DoctorBeryl/Braillescan-Mesh-Translator/braille-scan-1785328133079/img-1785328105541.jpg

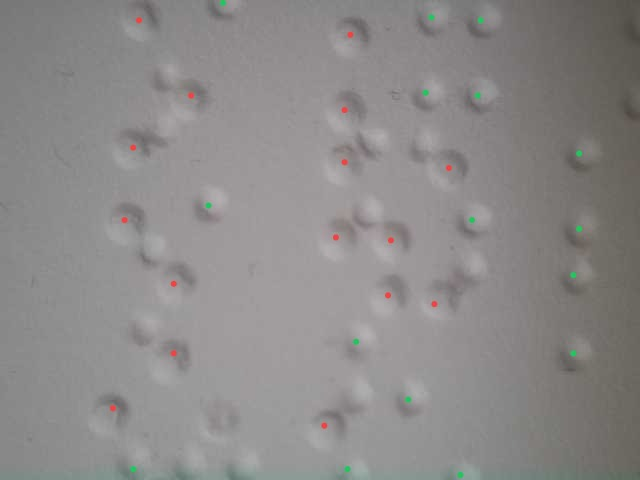
braille-scan-1785328133079/img-1785328105541.jpg
