DoctorBeryl/Braillescan-Mesh-Translator/braille-stitched-fixed/piece_0007.jpg

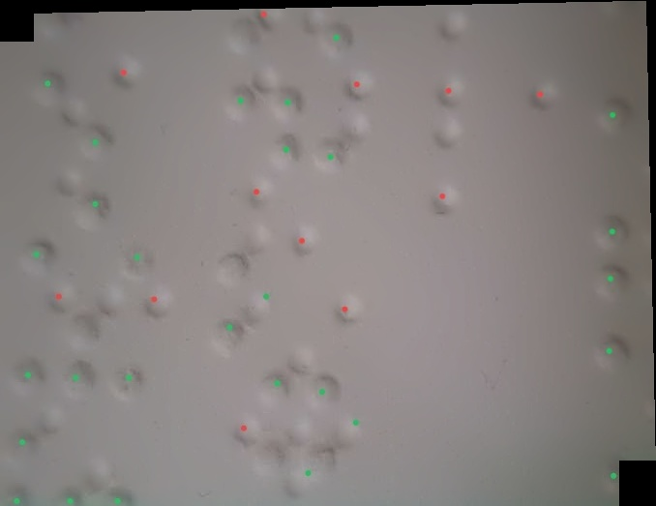
braille-stitched-fixed/piece_0007.jpg
