DoctorBeryl/Braillescan-Mesh-Translator/src/braille-scan-1785320781047/img-1785320766960.jpg

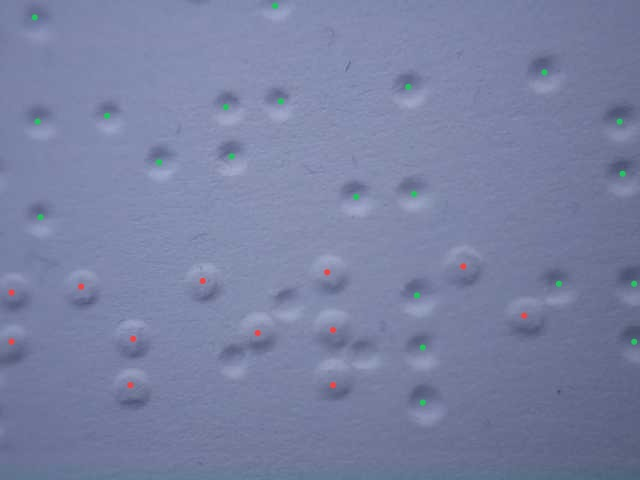
src/braille-scan-1785320781047/img-1785320766960.jpg
