DoctorBeryl/Braillescan-Mesh-Translator/test_images/input/img-1785227992667.jpg

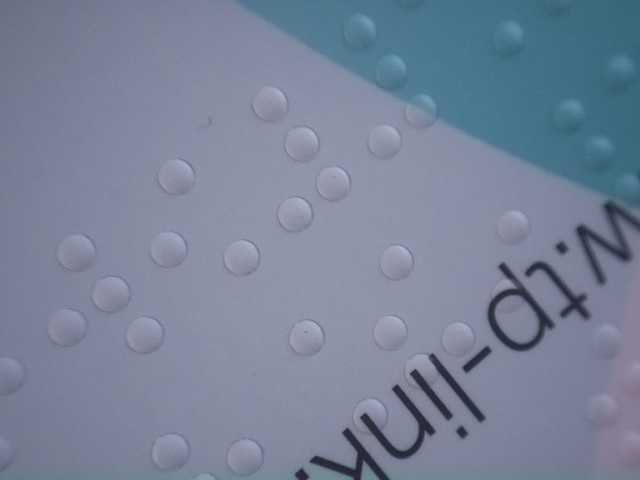
test_images/input/img-1785227992667.jpg
