DoctorBeryl/Braillescan-Mesh-Translator/test_images/output/crop2_topright.jpg

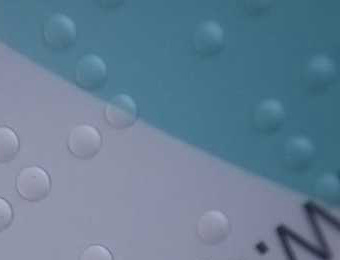
test_images/output/crop2_topright.jpg
