DoctorBeryl/Braillescan-Mesh-Translator/test_images/output/crop3_topright.jpg

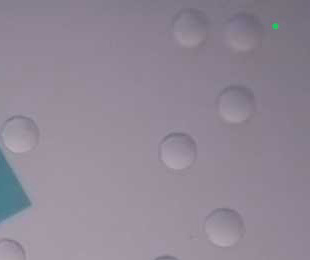
test_images/output/crop3_topright.jpg
