DoctorBeryl/Braillescan-Mesh-Translator/test_images/output_new/piece_0001.jpg

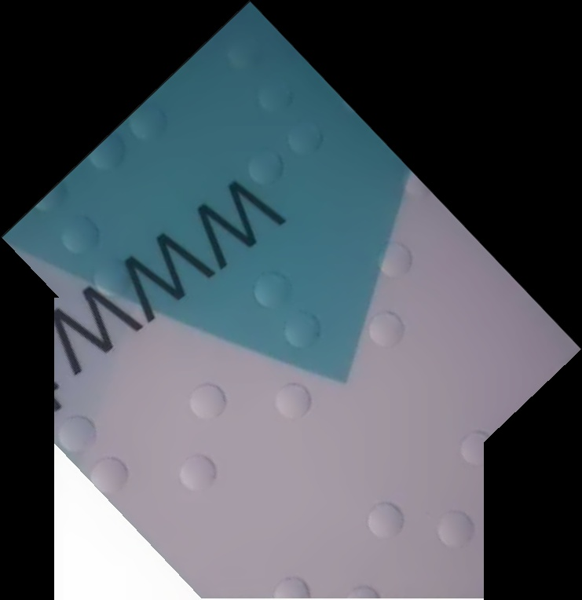
test_images/output_new/piece_0001.jpg
